hutoroff/TetrisEarrings/Core/Inc/work.h

#ifndef INC_WORK_H_
#define INC_WORK_H_

#ifdef __cplusplus
extern "C" {
#endif

//----------------------- includes -------------------------------------------//
#include "saportAndData.h"
#include "games.h"
#include "effects.h"
#include "ledMatrix.h"
//----------------------- defines --------------------------------------------//
#define MODE_STEP  8

//----------------------- function declarations ------------------------------//
void doWork (void);
void Work (void);

//----------------------- struct declarations --------------------------------//




#ifdef __cplusplus
}
#endif

#endif /* INC_WORK_H_ */
