hutoroff/TetrisEarrings/Core/Src/saportAndData.c

#include "saportAndData.h"

//----------------------- variables from this file -----------------------------------//
AppState state;   // Physically allocate 125 bytes in RAM
//------------------------------ functions -------------------------------------------//

//------------------------------ notes -------------------------------------------------//
